sqfmi/badgy/examples/grayscale/grayscale.h

/*
	You can convert your own image using the Image2Lcd tool https://www.waveshare.com/wiki/File:Image2Lcd.7z

	Output file type: C array
	Scan mode: Vertical scan
	BitsPixel: 16 Color
	Max Width: 296
	Max Height: 128
	Scan Right to Left: Checked
	Reverse Color: Checked
	Mirroring: Normal
	
*/
const unsigned char image[18944] = { /* 0X81,0X04,0X28,0X01,0X80,0X00, */
0X00,0X00,0X00,0X00,0X00,0X00,0X00,0X00,0X00,0X00,0X00,0X00,0X00,0X00,0X00,0X00,
0X00,0X00,0X00,0X00,0X00,0X00,0X00,0X00,0X00,0X00,0X00,0X00,0X00,0X00,0X00,0X00,
0X00,0X00,0X00,0X00,0X00,0X00,0X00,0X00,0X00,0X00,0X00,0X00,0X00,0X00,0X00,0X00,
0X00,0X00,0X00,0X00,0X00,0X00,0X00,0X00,0X00,0X00,0X00,0X00,0X00,0X00,0X00,0X00,
0X00,0X00,0X00,0X00,0X00,0X00,0X00,0X00,0X00,0X00,0X00,0X00,0X00,0X00,0X00,0X00,
0X00,0X00,0X00,0X00,0X00,0X00,0X00,0X00,0X00,0X00,0X00,0X00,0X00,0X00,0X00,0X00,
0X00,0X00,0X00,0X00,0X00,0X00,0X00,0X00,0X00,0X00,0X00,0X00,0X00,0X00,0X00,0X00,
0X00,0X00,0X00,0X00,0X00,0X00,0X00,0X00,0X00,0X00,0X00,0X00,0X00,0X00,0X00,0X00,
0X00,0X00,0X00,0X00,0X00,0X00,0X00,0X00,0X00,0X00,0X00,0X00,0X00,0X00,0X00,0X00,
0X00,0X00,0X00,0X00,0X00,0X00,0X00,0X00,0X00,0X00,0X00,0X00,0X00,0X00,0X00,0X00,
0X00,0X00,0X00,0X00,0X00,0X00,0X00,0X00,0X00,0X00,0X00,0X00,0X00,0X00,0X00,0X00,
0X00,0X00,0X00,0X00,0X00,0X00,0X00,0X00,0X00,0X00,0X00,0X00,0X00,0X00,0X00,0X00,
0X00,0X00,0X00,0X00,0X00,0X00,0X00,0X00,0X00,0X00,0X00,0X00,0X00,0X00,0X00,0X00,
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
};

const unsigned char lut_bb[] ={
0x80	,0x0A	,0x00	,0x00	,0x00	,0x01,
0x90	,0x14	,0x14	,0x00	,0x00	,0x01,
0x20	,0x14	,0x0A	,0x00	,0x00	,0x01,
0x50	,0x13	,0x01	,0x00	,0x00	,0x01,
0x00	,0x00	,0x00	,0x00	,0x00	,0x00,
0x00	,0x00	,0x00	,0x00	,0x00	,0x00,
0x00	,0x00	,0x00	,0x00	,0x00	,0x00,
};
