sqfmi/badgy/examples/weather/icons.h

/* OpenWeatherMap Weather Conditions Code */
/*******************************************
Group 2xx: Thunderstorm
ID	Meaning	Icon
200	thunderstorm with light rain	 	wi-thunderstorm
201	thunderstorm with rain	 			wi-thunderstorm
202	thunderstorm with heavy rain	 	wi-thunderstorm
210	light thunderstorm					wi-thunderstorm
211	thunderstorm	 					wi-thunderstorm
212	heavy thunderstorm	 				wi-thunderstorm
221	ragged thunderstorm	 				wi-thunderstorm
230	thunderstorm with light drizzle	 	wi-thunderstorm
231	thunderstorm with drizzle	 		wi-thunderstorm
232	thunderstorm with heavy drizzle	 	wi-thunderstorm
Group 3xx: Drizzle
ID	Meaning	Icon
300	light intensity Drizzle 			wi-showers
301	drizzle	 							wi-showers
302	heavy intensity drizzle	 			wi-showers
310	light intensity drizzle rain	 	wi-showers
311	drizzle rain	 					wi-showers
312	heavy intensity drizzle rain	 	wi-showers
313	shower rain and drizzle	 			wi-showers
314	heavy shower rain and drizzle	 	wi-showers
321	shower drizzle	 					wi-showers
Group 5xx: Rain
ID	Meaning	Icon
500	light rain	 						wi-rain
501	moderate rain	 					wi-rain
502	heavy intensity rain	 			wi-rain
503	very heavy rain	 					wi-rain
504	extreme rain	 					wi-rain
511	freezing rain	 					wi-rain
520	light intensity shower rain	 		wi-rain
521	shower rain	 						wi-rain
522	heavy intensity shower rain	 		wi-rain
531	ragged shower rain	 				wi-rain
Group 6xx: Snow
ID	Meaning	Icon
600	light snow	 						wi-snow
601	snow	 							wi-snow
602	heavy snow	 						wi-snow
611	sleet	 							wi-sleet
612	shower sleet	 					wi-sleet
615	light rain and snow	 				wi-rain-mix
616	rain and snow	 					wi-rain-mix
620	light shower snow	 				wi-rain-mix
621	shower snow	 						wi-rain-mix
622	heavy shower snow	 				wi-rain-mix
Group 7xx: Atmosphere
ID	Meaning	Icon
701	mist	 							wi-fog
711	smoke	 							wi-smoke
721	haze	 							wi-fog
731	sand, dust whirls	 				wi-sandstorm
741	fog	 								wi-fog
751	sand	 							wi-dust
761	dust	 							wi-dust
762	volcanic ash	 					wi-volcano
771	squalls	 							wi-strong-wind
781	tornado	 							wi-tornado
Group 800: Clear
ID	Meaning	Icon
800	clear sky	 						wi-day-sunny  wi-night-clear
Group 80x: Clouds
ID	Meaning	Icon
801	few clouds	 						wi-day-cloudy  	wi-night-cloudy
802	scattered clouds	 				wi-day-cloudy  	wi-night-cloudy
803	broken clouds	 					wi-cloudy 		wi-night-cloudy
804	overcast clouds	 					wi-cloudy  		wi-night-cloudy
*******************************************/

/* Weather icons generated from https://github.com/erikflowers/weather-icons */

// 'wi-celsius', 48x48px
const unsigned char celsius [] PROGMEM = {
	0xff, 0xff, 0xff, 0xff, 0xff, 0xff, 0xff, 0xff, 0xff, 0xff, 0xff, 0xff, 0xff, 0xff, 0xff, 0xff, 
	0xff, 0xff, 0xff, 0xff, 0xff, 0xff, 0xff, 0xff, 0xff, 0xff, 0xff, 0xff, 0xff, 0xff, 0xff, 0xff, 
	0xff, 0xff, 0xff, 0xff, 0xff, 0xff, 0xff, 0xff, 0xff, 0xff, 0xff, 0xff, 0xff, 0xff, 0xff, 0xff, 
	0xff, 0xff, 0xff, 0xff, 0xff, 0xff, 0xff, 0xff, 0xff, 0xff, 0xff, 0xff, 0xff, 0xff, 0xff, 0xff, 
	0xff, 0xff, 0xff, 0xff, 0xff, 0xff, 0xff, 0xff, 0xff, 0xff, 0xff, 0xff, 0xff, 0xff, 0xff, 0xff, 
	0xff, 0xff, 0xff, 0xff, 0xff, 0xff, 0xdf, 0xc3, 0xff, 0xff, 0xff, 0xff, 0x07, 0x80, 0xff, 0xff, 
	0xff, 0xff, 0x27, 0x00, 0xff, 0xff, 0xff, 0xfe, 0x72, 0x3c, 0x7f, 0xff, 0xff, 0xfe, 0x22, 0x7f, 
	0xff, 0xff, 0xff, 0xff, 0x06, 0x7f, 0xff, 0xff, 0xff, 0xff, 0x8e, 0x7f, 0xff, 0xff, 0xff, 0xff, 
	0xfe, 0x7f, 0xff, 0xff, 0xff, 0xff, 0xfe, 0x7f, 0xff, 0xff, 0xff, 0xff, 0xfe, 0x7f, 0xff, 0xff, 
	0xff, 0xff, 0xfe, 0x7f, 0xff, 0xff, 0xff, 0xff, 0xfe, 0x7f, 0xff, 0xff, 0xff, 0xff, 0xfe, 0x3c, 
	0x7f, 0xff, 0xff, 0xff, 0xff, 0x10, 0xff, 0xff, 0xff, 0xff, 0xff, 0x00, 0xff, 0xff, 0xff, 0xff, 
	0xff, 0xc3, 0xff, 0xff, 0xff, 0xff, 0xff, 0xff, 0xff, 0xff, 0xff, 0xff, 0xff, 0xff, 0xff, 0xff, 
	0xff, 0xff, 0xff, 0xff, 0xff, 0xff, 0xff, 0xff, 0xff, 0xff, 0xff, 0xff, 0xff, 0xff, 0xff, 0xff, 
	0xff, 0xff, 0xff, 0xff, 0xff, 0xff, 0xff, 0xff, 0xff, 0xff, 0xff, 0xff, 0xff, 0xff, 0xff, 0xff, 
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
	0xff, 0x03, 0x6c, 0xff, 0xff, 0x82, 0x2d, 0xff, 0xff, 0x86, 0x39, 0xff, 0xff, 0xc0, 0x03, 0xff, 
	0xff, 0xe0, 0x07, 0xff, 0xff, 0xf8, 0x1f, 0xff, 0xff, 0xff, 0xff, 0xff, 0xff, 0xff, 0xff, 0xff, 
	0xff, 0xff, 0xff, 0xff, 0xff, 0xff, 0xff, 0xff, 0xff, 0xff, 0xff, 0xff, 0xff, 0xff, 0xff, 0xff
};
